vives-project-xp/EOMarkers/Affiche/product_1.jpg

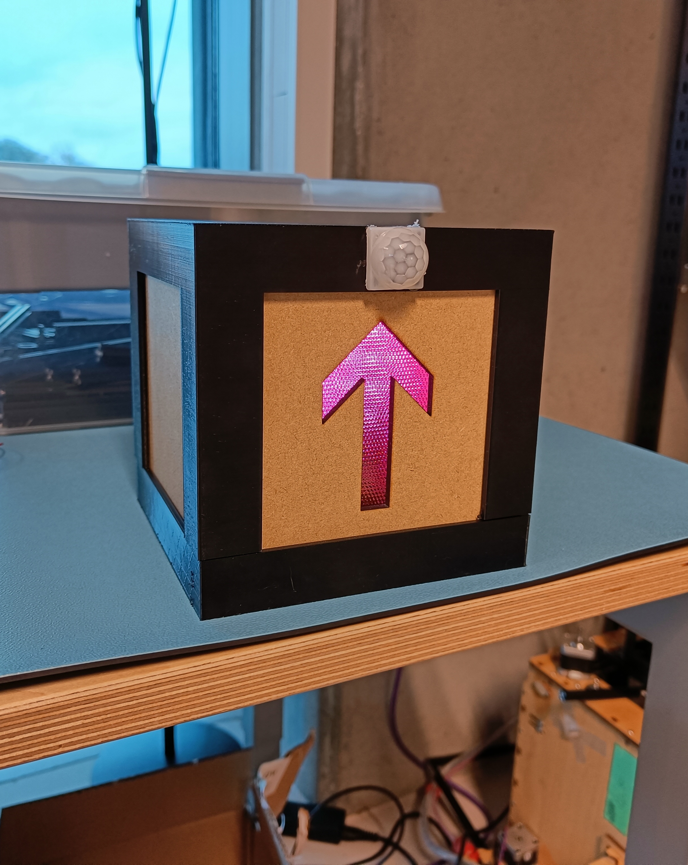
Affiche/product_1.jpg
