vives-project-xp/EOMarkers/Affiche/product_2.jpg

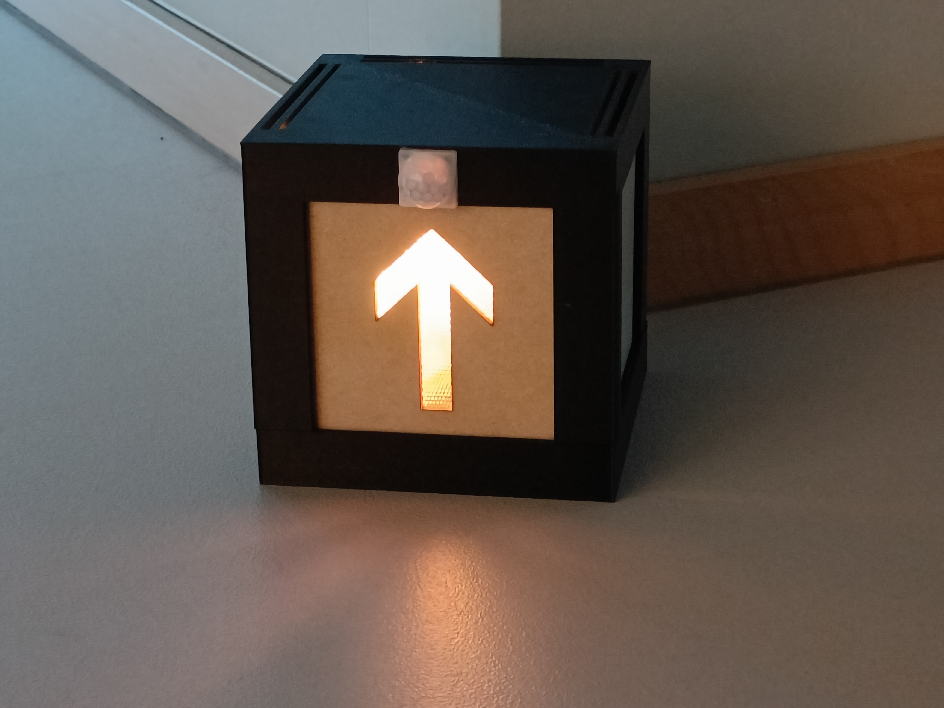
Affiche/product_2.jpg
