vives-project-xp/EOMarkers/Affiche/product_3.jpg

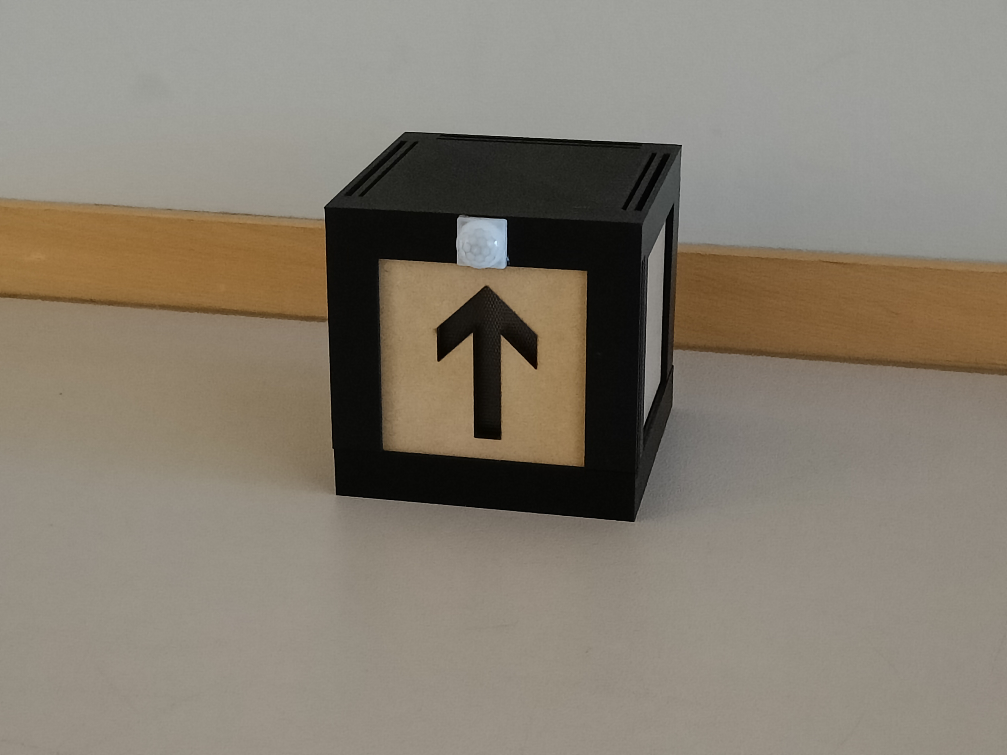
Affiche/product_3.jpg
