vives-project-xp/EOMarkers/Affiche/product_4.jpg

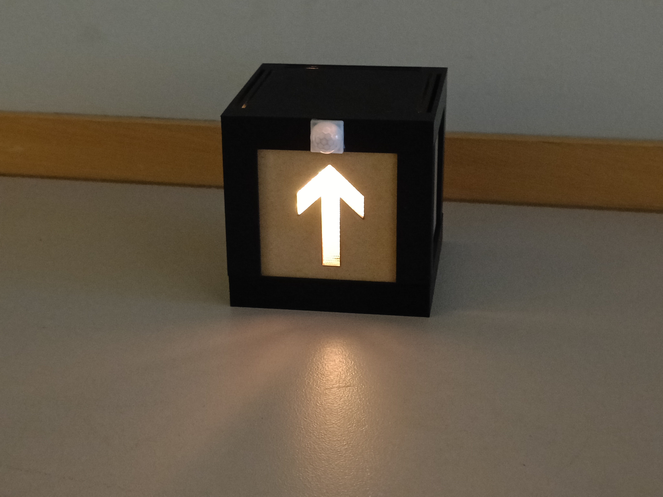
Affiche/product_4.jpg
