vives-project-xp/EOMarkers/img/qr.png

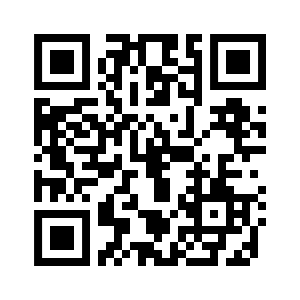
img/qr.png
