vives-project-xp/EOMarkers/PCB/details.png

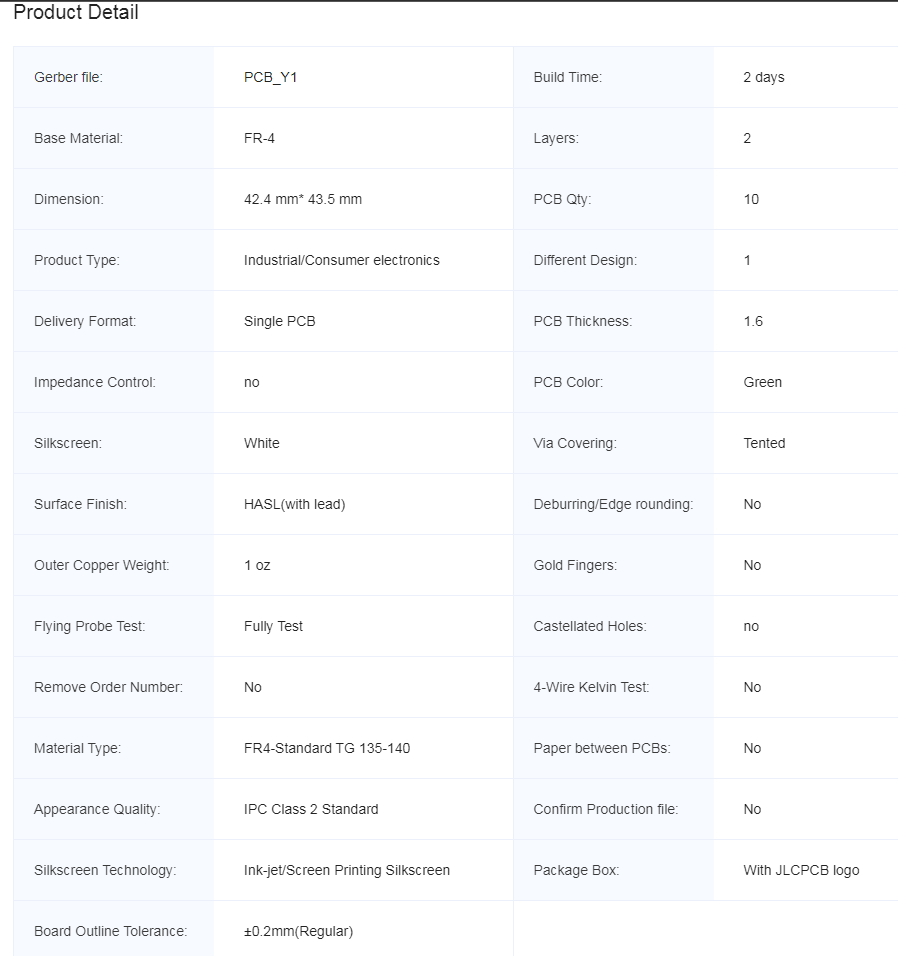
PCB/details.png
